alken01/ee-plant/SolidWorks/drawings/PlantCover.DXF

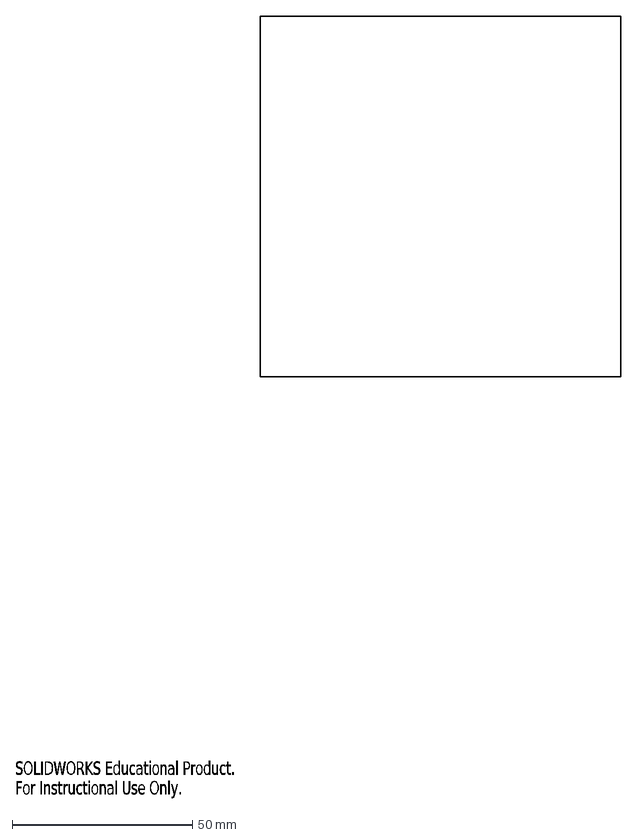
[picture p18: CAD file, 2022-05-12]
SolidWorks/drawings/PlantCover.DXF
SOLIDWORKS Educational Product.
For Instructional Use Only.
