alken01/ee-plant/SolidWorks/Parts/ReservoirFrontNoHoles.SLDPRT

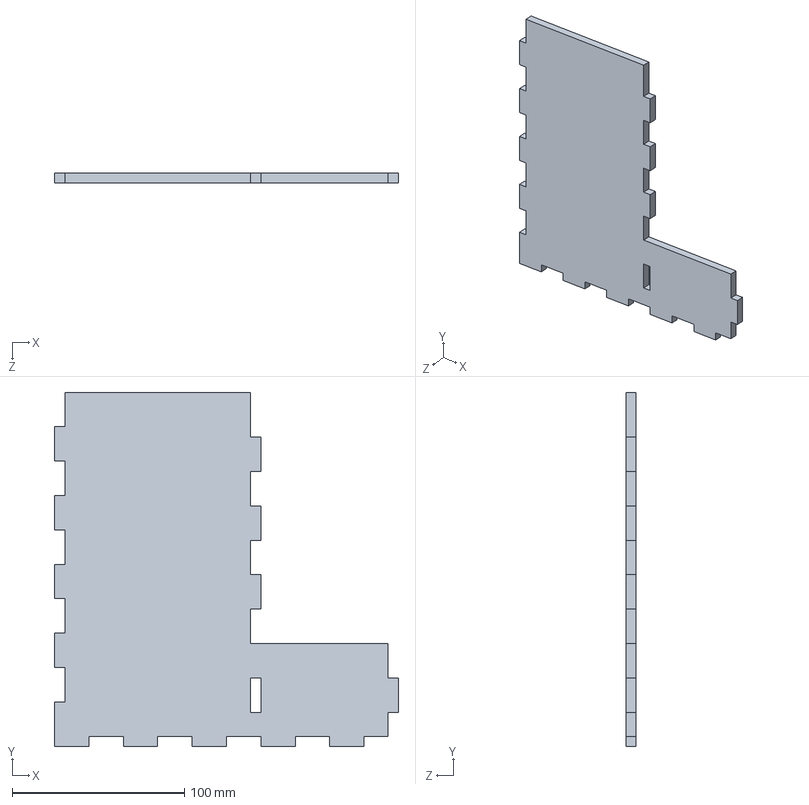
[picture p19: CAD file, 2022-05-12]
SolidWorks/Parts/ReservoirFrontNoHoles.SLDPRT
200.0 x 206.0 x 6.00 mm
