alken01/ee-plant/SolidWorks/drawings/ReservoirCover.DXF

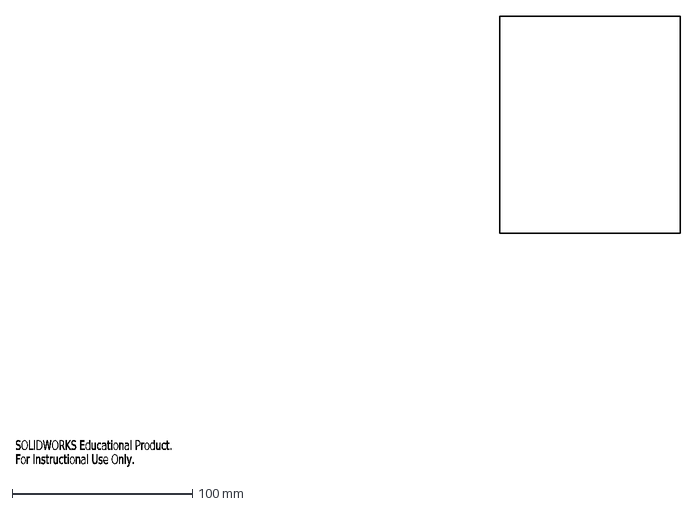
[picture p20: CAD file, 2022-05-12]
SolidWorks/drawings/ReservoirCover.DXF
SOLIDWORKS Educational Product.
For Instructional Use Only.
