alken01/ee-plant/SolidWorks/Parts/ElectronicsCover.SLDPRT

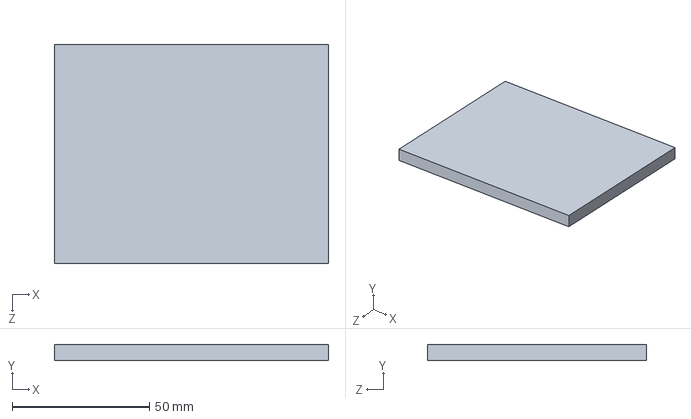
[picture p21: CAD file, 2022-05-12]
SolidWorks/Parts/ElectronicsCover.SLDPRT
100.0 x 6.00 x 80.0 mm
