alken01/ee-plant/SolidWorks/drawings/ElectronicsCover.DXF

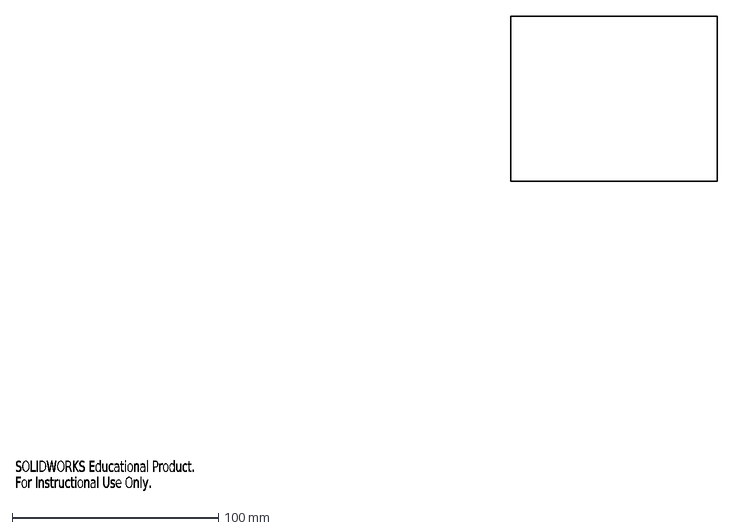
[picture p22: CAD file, 2022-05-12]
SolidWorks/drawings/ElectronicsCover.DXF
SOLIDWORKS Educational Product.
For Instructional Use Only.
