alken01/ee-plant/SolidWorks/Parts/ReservoirFront.SLDPRT

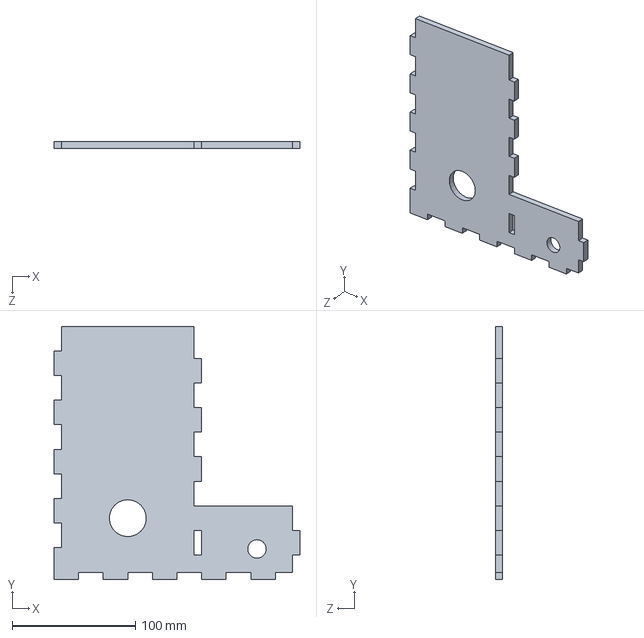
[picture p23: CAD file, 2022-05-12]
SolidWorks/Parts/ReservoirFront.SLDPRT
200.0 x 206.0 x 6.00 mm
