alken01/ee-plant/SolidWorks/drawings/ReservoirFrontNoHoles.DXF

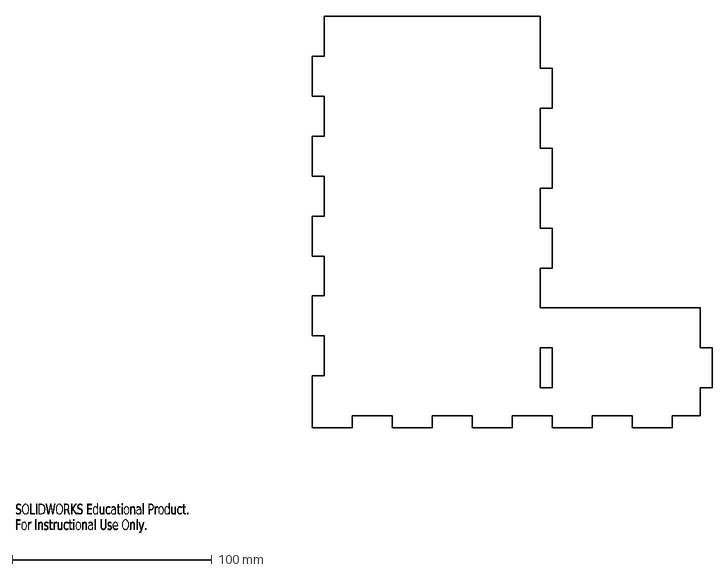
[picture p24: CAD file, 2022-05-12]
SolidWorks/drawings/ReservoirFrontNoHoles.DXF
SOLIDWORKS Educational Product.
For Instructional Use Only.
