alken01/ee-plant/SolidWorks/Parts/PlantBack.SLDPRT

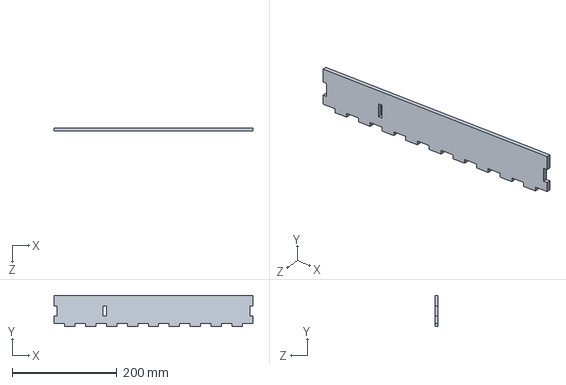
[picture p25: CAD file, 2022-05-12]
SolidWorks/Parts/PlantBack.SLDPRT
380.0 x 60.0 x 6.00 mm
