alken01/ee-plant/SolidWorks/drawings/ReservoirSExtraLong.DXF

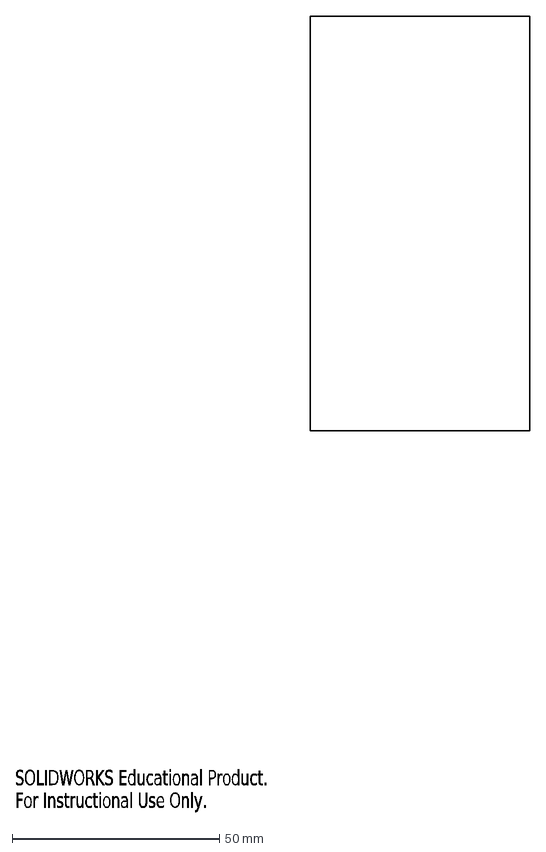
[picture p26: CAD file, 2022-05-12]
SolidWorks/drawings/ReservoirSExtraLong.DXF
SOLIDWORKS Educational Product.
For Instructional Use Only.
