alken01/ee-plant/SolidWorks/Parts/PlantSide.SLDPRT

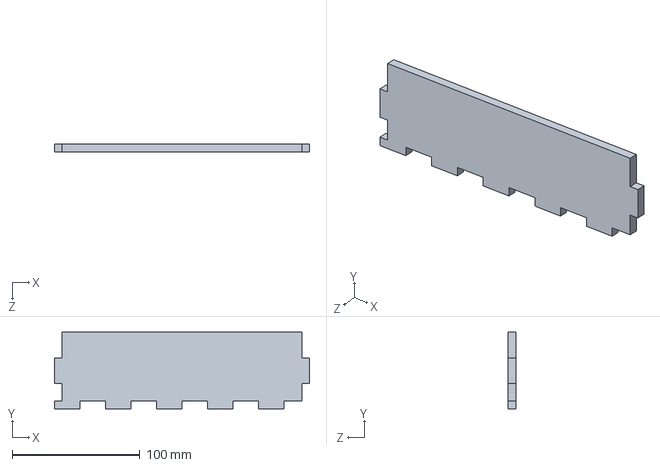
[picture p27: CAD file, 2022-05-12]
SolidWorks/Parts/PlantSide.SLDPRT
200.0 x 60.0 x 6.00 mm
