alken01/ee-plant/SolidWorks/drawings/PlantSide.DXF

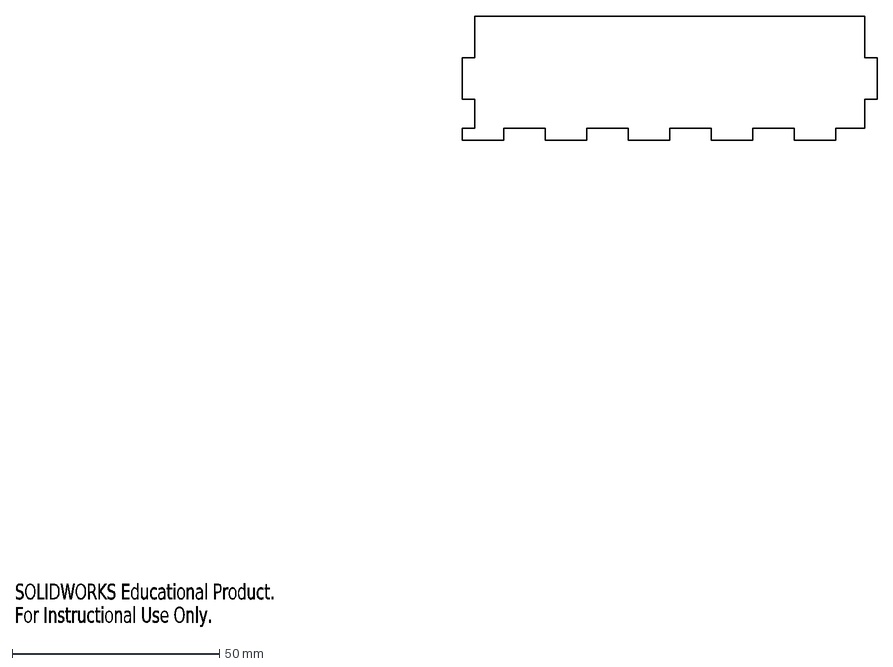
[picture p28: CAD file, 2022-05-12]
SolidWorks/drawings/PlantSide.DXF
SOLIDWORKS Educational Product.
For Instructional Use Only.
