alken01/ee-plant/SolidWorks/Parts/MDFSide.SLDPRT

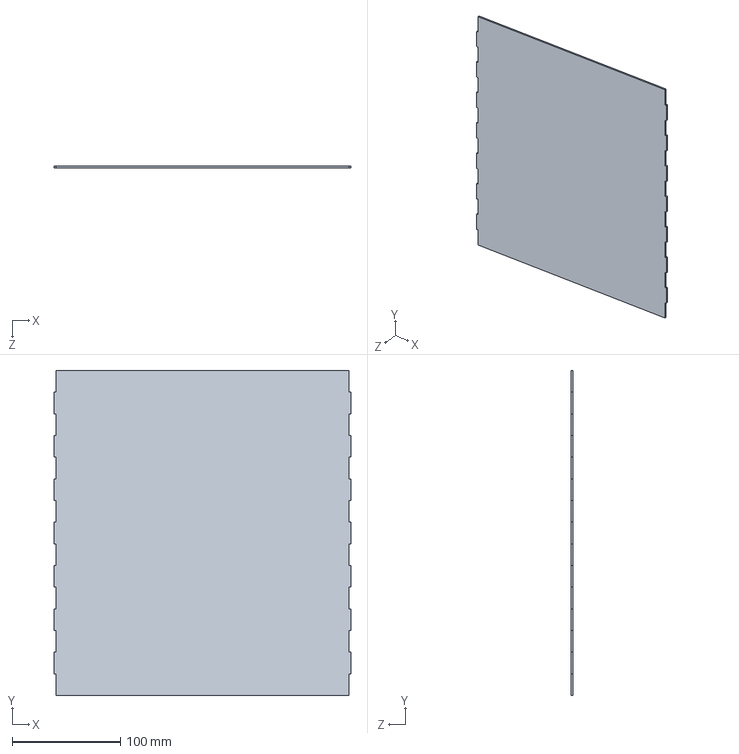
[picture p29: CAD file, 2022-05-12]
SolidWorks/Parts/MDFSide.SLDPRT
274.0 x 300.0 x 2.00 mm
