alken01/ee-plant/SolidWorks/Parts/PlexiFrontNoHOles.SLDPRT

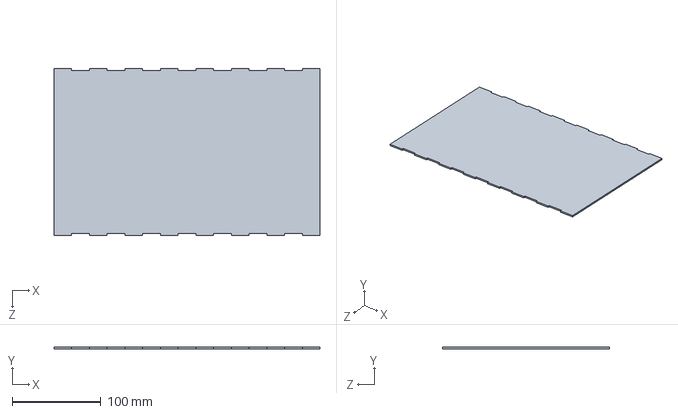
[picture p30: CAD file, 2022-05-12]
SolidWorks/Parts/PlexiFrontNoHOles.SLDPRT
300.0 x 2.00 x 188.0 mm
