alken01/ee-plant/SolidWorks/Parts/PlexiCover.SLDPRT

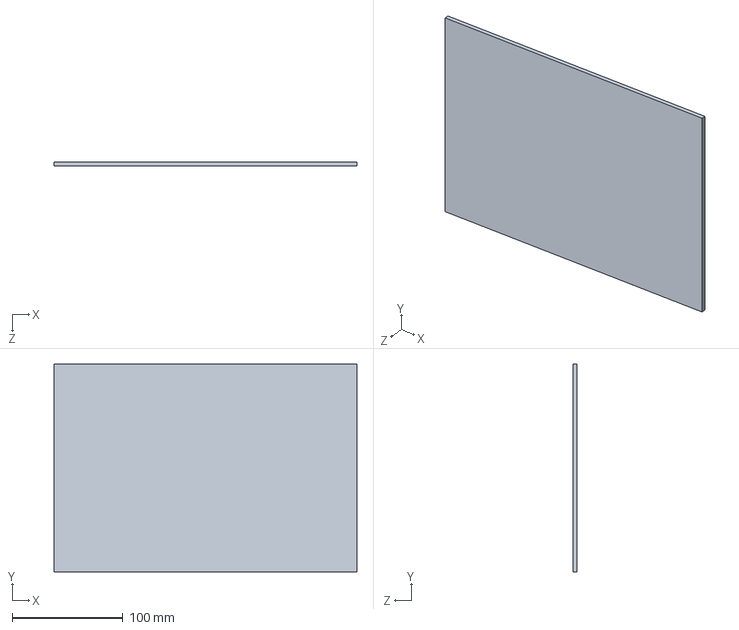
[picture p31: CAD file, 2022-05-12]
SolidWorks/Parts/PlexiCover.SLDPRT
274.0 x 188.0 x 4.00 mm
