alken01/ee-plant/SolidWorks/Parts/ElectronicsFrontBack.SLDPRT

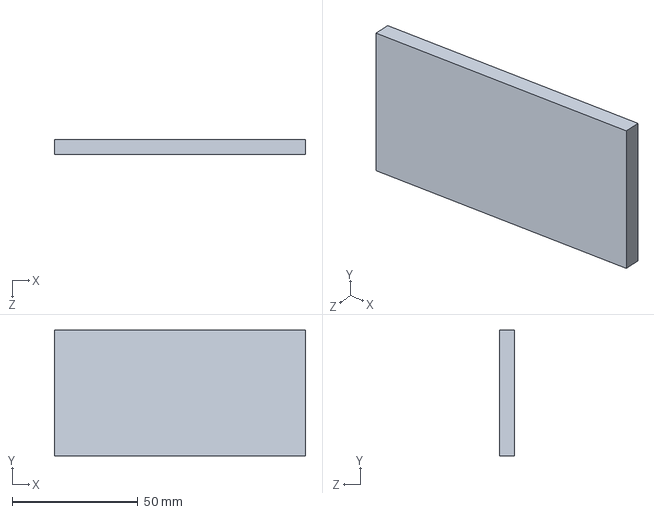
[picture p32: CAD file, 2022-05-12]
SolidWorks/Parts/ElectronicsFrontBack.SLDPRT
100.0 x 50.0 x 6.00 mm
