alken01/ee-plant/SolidWorks/Parts/ReservoirS.SLDPRT

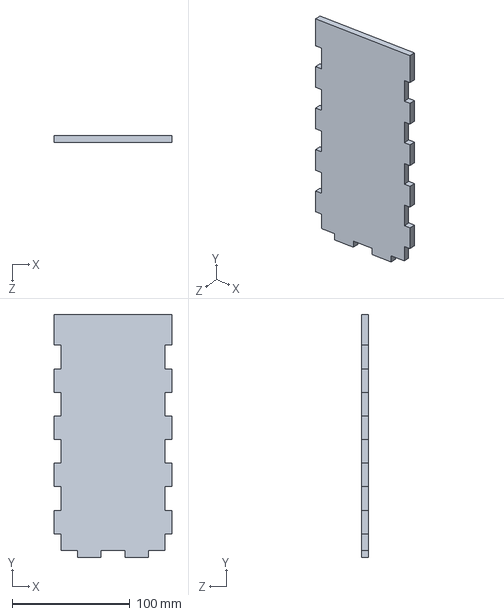
[picture p33: CAD file, 2022-05-12]
SolidWorks/Parts/ReservoirS.SLDPRT
100.0 x 206.0 x 6.00 mm
