alken01/ee-plant/SolidWorks/Parts/PlantBottom.SLDPRT

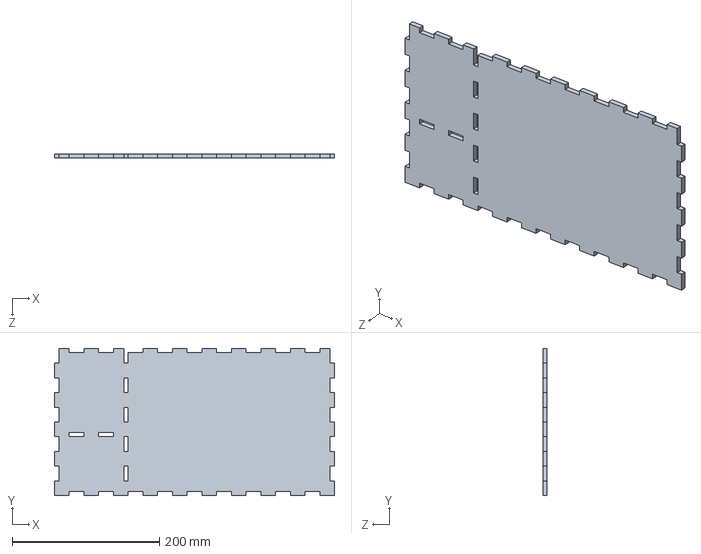
[picture p34: CAD file, 2022-05-12]
SolidWorks/Parts/PlantBottom.SLDPRT
380.0 x 200.0 x 6.00 mm
